JordanAceto/quad_ADSR_board/firmware/BSP/interrupts.c

/*
--|----------------------------------------------------------------------------|
--| FILE DESCRIPTION:
--|   interrupts.h provides the implementation for the interrupts used by the 
--|   system.
--|   
--|  
--|----------------------------------------------------------------------------|
--| REFERENCES:
--|
--|----------------------------------------------------------------------------|
*/

/*
--|----------------------------------------------------------------------------|
--| INCLUDE FILES
--|----------------------------------------------------------------------------|
*/

#include "interrupts.h"
#include "stm32f4xx.h"

/*
--|----------------------------------------------------------------------------|
--| PRIVATE DEFINES
--|----------------------------------------------------------------------------|
*/

// note that for interrupts, higher numbers mean lower priority

/*
--| NAME: TIM6_IRQ_PRIORITY
--| DESCRIPTION: the priority of the TIM6 interrupt
--| TYPE: uint
*/
#define TIM6_IRQ_PRIORITY (0)

/*
--| NAME: TIM6_IRQ_PRIORITY
--| DESCRIPTION: the priority of the TIM7 interrupt
--| TYPE: uint
*/
#define TIM7_IRQ_PRIORITY (1)

/*
--|----------------------------------------------------------------------------|
--| PRIVATE VARIABLES
--|----------------------------------------------------------------------------|
*/

/*
--| NAME: flags
--| DESCRIPTION: the interrupt flags used by the system
--| TYPE: bool
*/
static volatile bool flags[NUM_INTERRUPT_FLAG_TYPES];

/*
--|----------------------------------------------------------------------------|
--| PRIVATE HELPER FUNCTION PROTOTYPES
--|----------------------------------------------------------------------------|
*/

/*------------------------------------------------------------------------------
Function Name:
    interrupt_set_flag

Function Description:
    Set the specified interrupt flag.

Parameters:
    flag: the flag to set

Returns:
    None

Assumptions/Limitations:
    Assumed that the flag is a member of the Interrupt_Flag_t enumeration.
------------------------------------------------------------------------------*/
void interrupt_set_flag(Interrupt_Flag_t flag);

/*------------------------------------------------------------------------------
Function Name:
    interrupt_clear_flag

Function Description:
    Clear the specified interrupt flag.

Parameters:
    flag: the flag to clear

Returns:
    None

Assumptions/Limitations:
    Assumed that the flag is a member of the Interrupt_Flag_t enumeration.
------------------------------------------------------------------------------*/
void interrupt_clear_flag(Interrupt_Flag_t flag);

/*------------------------------------------------------------------------------
Function Name:
    TIM6_DAC_IRQHandler

Function Description:
    IRQ handler for the TIM6 interrupt.

Parameters:
    None

Returns:
    None

Assumptions/Limitations:
    Called automatically, do not call this function.
------------------------------------------------------------------------------*/
void TIM6_DAC_IRQHandler(void);

/*------------------------------------------------------------------------------
Function Name:
    TIM7_IRQHandler

Function Description:
    IRQ handler for the TIM7 interrupt.

Parameters:
    None

Returns:
    None

Assumptions/Limitations:
    Called automatically, do not call this function.
------------------------------------------------------------------------------*/
void TIM7_IRQHandler(void);

/*
--|----------------------------------------------------------------------------|
--| PUBLIC FUNCTION DEFINITIONS
--|----------------------------------------------------------------------------|
*/

void interrupts_Init(void)
{
    // enable the TIM6 IRQ
    NVIC_SetPriority(TIM6_DAC_IRQn, TIM6_IRQ_PRIORITY);
    NVIC_EnableIRQ(TIM6_DAC_IRQn);

    // enable the TIM7 IRQ
    NVIC_SetPriority(TIM7_IRQn, TIM7_IRQ_PRIORITY);
    NVIC_EnableIRQ(TIM7_IRQn);
}

bool interrupt_get_flag(Interrupt_Flag_t flag)
{
    const bool retval = flags[flag];
    interrupt_clear_flag(flag);
    return retval;
}

/*
--|----------------------------------------------------------------------------|
--| PRIVATE HELPER FUNCTION DEFINITIONS
--|----------------------------------------------------------------------------|
*/

void interrupt_set_flag(Interrupt_Flag_t flag)
{
    flags[flag] = true;
}

void interrupt_clear_flag(Interrupt_Flag_t flag)
{
    flags[flag] = false;
}

void TIM6_DAC_IRQHandler(void)
{
    interrupt_set_flag(INTERRUPT_FLAG_TIM6);

    // clear the Update Interrupt flag in the status register
    TIM6->SR &= ~TIM_SR_UIF;
}

void TIM7_IRQHandler(void)
{
    interrupt_set_flag(INTERRUPT_FLAG_TIM7);
    
    // clear the Update Interrupt flag in the status register
    TIM7->SR &= ~TIM_SR_UIF;
}
