JordanAceto/quad_ADSR_board/firmware/BSP/TIM6.h

/*
--|----------------------------------------------------------------------------|
--| FILE DESCRIPTION:
--|   TIM6.h provides the interface for initializing TIM6.
--|   
--|   TIM6 is configured as a periodic timer that sets the sample time for the
--|   high prioritry, relatively fast-updating tasks.
--|
--|----------------------------------------------------------------------------|
--| REFERENCES:
--|   STM32F4xx Reference Manual, page 696 (Basic Timers)
--|
--|----------------------------------------------------------------------------|
*/

#ifndef TIM6_H_INCLUDED
#define TIM6_H_INCLUDED

/*
--|----------------------------------------------------------------------------|
--| PUBLIC DEFINES
--|----------------------------------------------------------------------------|
*/

/*
--| NAME: TIM6_FREQUENCY_Hz
--| DESCRIPTION: the frequency of timer 6, in Hertz
--| TYPE: uint
*/
#define TIM6_FREQUENCY_Hz (5000u)

/*
--|----------------------------------------------------------------------------|
--| PUBLIC FUNCTION PROTOTYPES
--|----------------------------------------------------------------------------|
*/

/*------------------------------------------------------------------------------
Function Name:
    TIM6_Init

Function Description:
    Perform initialization of TIM6.

Parameters:
    None

Returns:
    None

Assumptions/Limitations:
    Assumed that this will be called before using TIM6.
------------------------------------------------------------------------------*/
void TIM6_Init(void);

#endif
